SkullKill/ESP32-Wall-Clock-PCB/ESP32-Wall-Clock/ESP32-Wall-Clock-Front-RT-V1.0a-WithOLEDboard.jpg

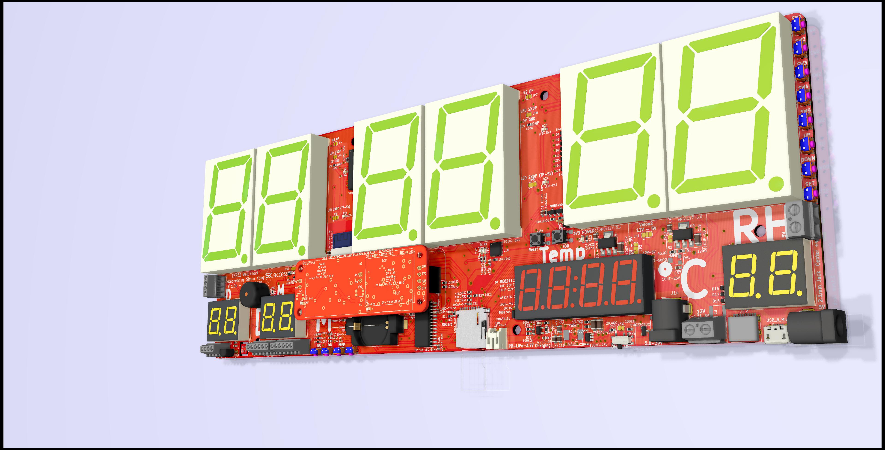
ESP32-Wall-Clock/ESP32-Wall-Clock-Front-RT-V1.0a-WithOLEDboard.jpg
