SkullKill/ESP32-Wall-Clock-PCB/ESP32-Wall-Clock/ESP32-Wall-Clock-Front-V1.0.jpg

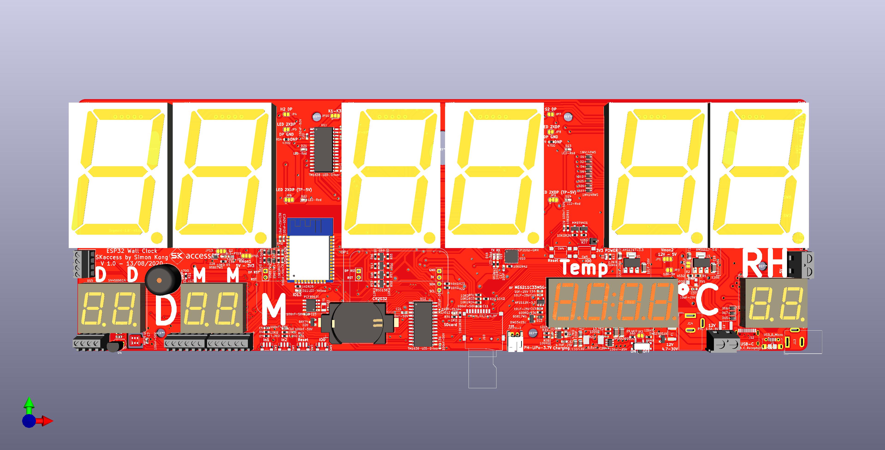
ESP32-Wall-Clock/ESP32-Wall-Clock-Front-V1.0.jpg
